XantaroDE/iC880A-Raspberry-PI/ch2i-orig/pictures/ch2i-gateway-monitoring-iot.jpg

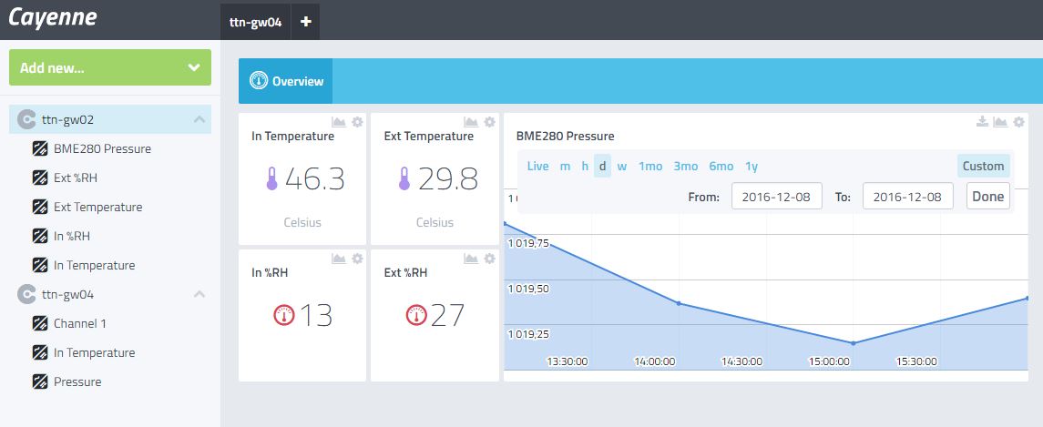
ch2i-orig/pictures/ch2i-gateway-monitoring-iot.jpg
