XantaroDE/iC880A-Raspberry-PI/ch2i-orig/pictures/ch2i-shield-lorawan-gateway.jpg

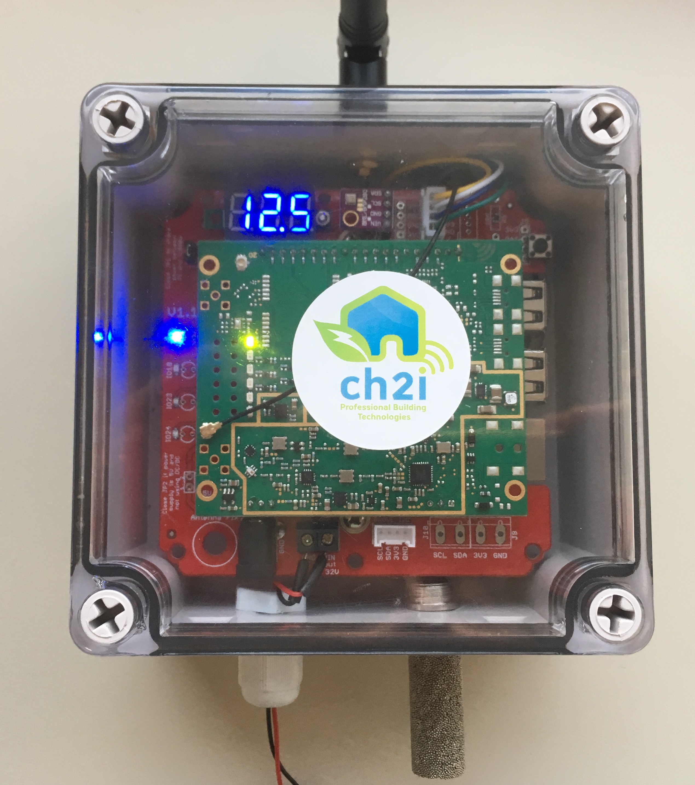
ch2i-orig/pictures/ch2i-shield-lorawan-gateway.jpg
