XantaroDE/iC880A-Raspberry-PI/ch2i-orig/pictures/iC880A-mounted-enclosure.jpg

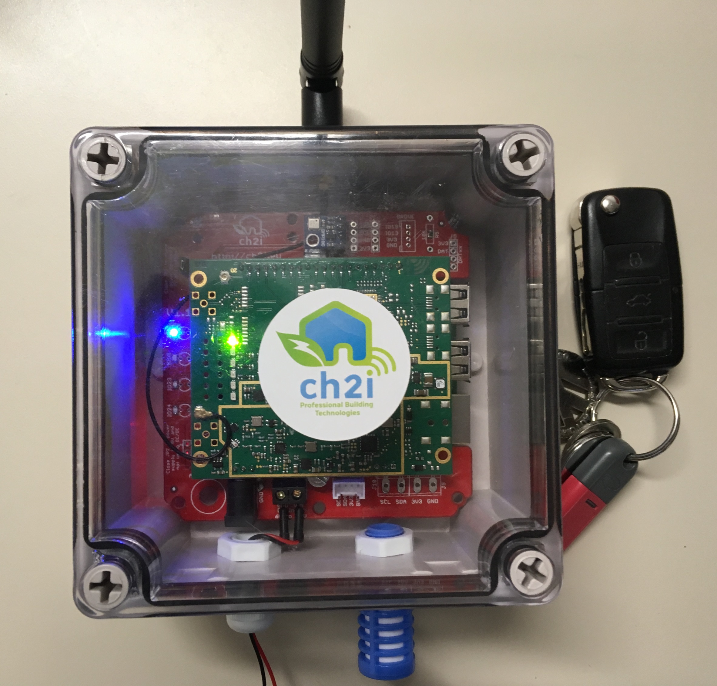
ch2i-orig/pictures/iC880A-mounted-enclosure.jpg
