XantaroDE/iC880A-Raspberry-PI/ch2i-orig/pictures/ic880a-mounted-V12.jpg

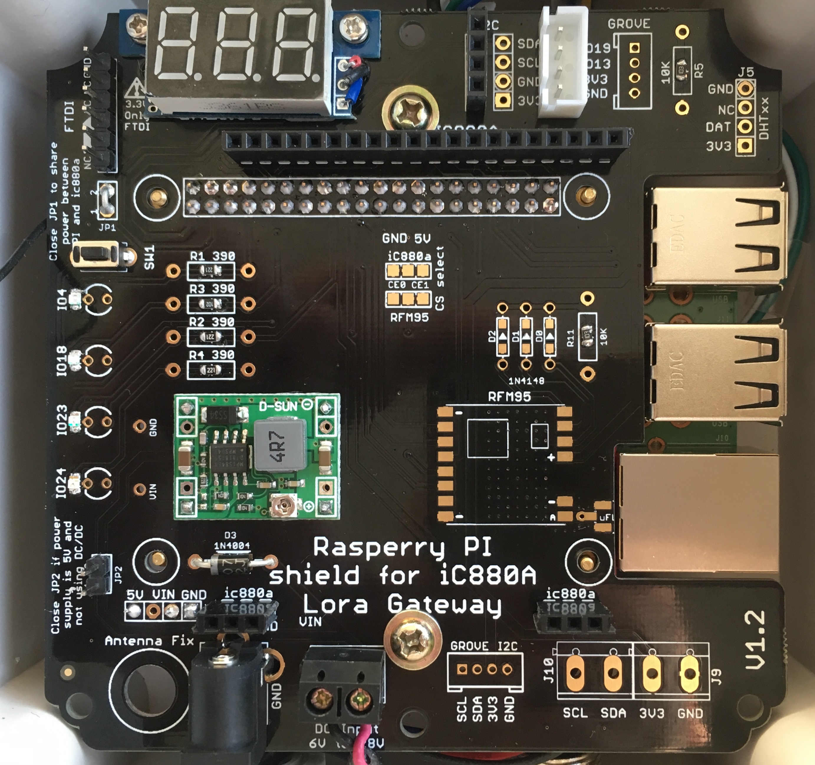
ch2i-orig/pictures/ic880a-mounted-V12.jpg
