XantaroDE/iC880A-Raspberry-PI/ch2i-orig/pictures/RPI-Lora-Gateway-mounted.jpg

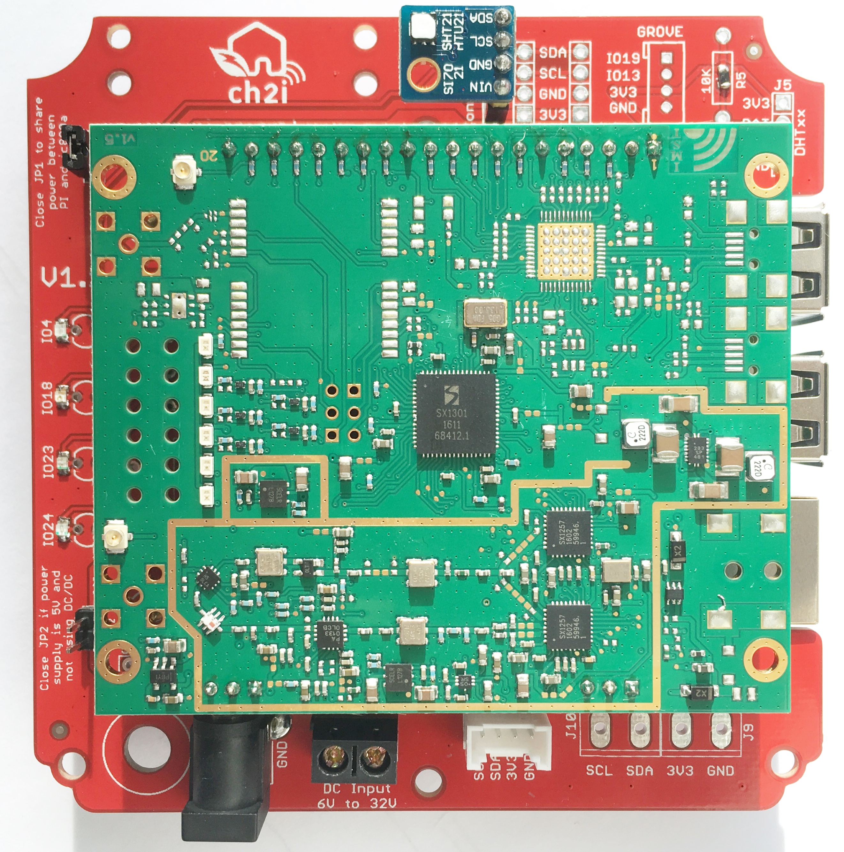
ch2i-orig/pictures/RPI-Lora-Gateway-mounted.jpg
