XantaroDE/iC880A-Raspberry-PI/ch2i-orig/pictures/RPI-Lora-Gateway-PCB.jpg

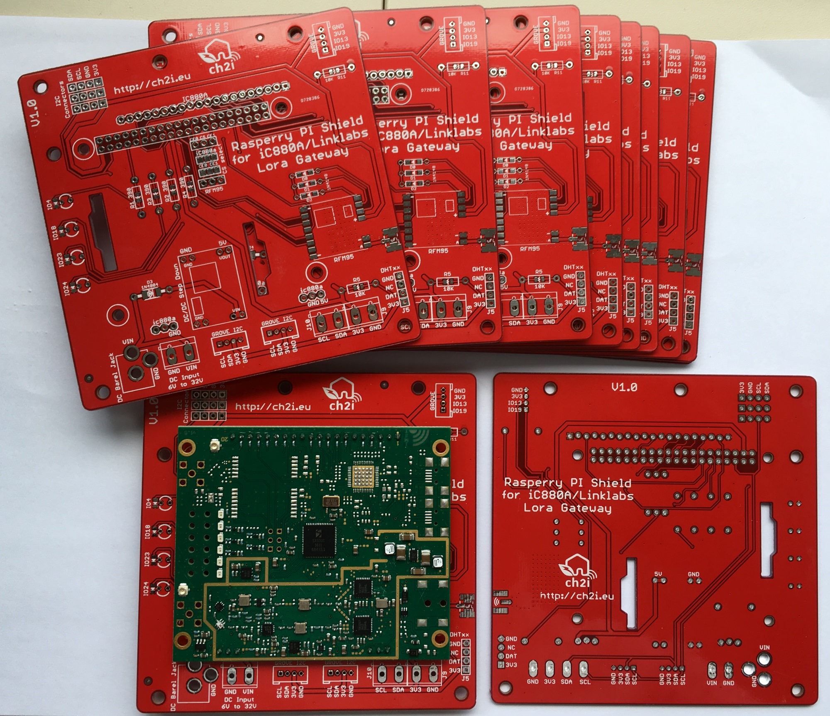
ch2i-orig/pictures/RPI-Lora-Gateway-PCB.jpg
