XantaroDE/iC880A-Raspberry-PI/ch2i-orig/pictures/RPI-Lora-Gateway-Shield-bot.png

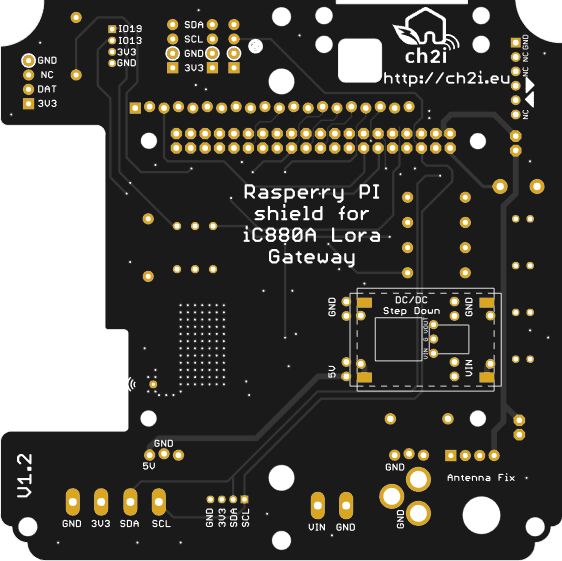
ch2i-orig/pictures/RPI-Lora-Gateway-Shield-bot.png
