XantaroDE/iC880A-Raspberry-PI/ch2i-orig/pictures/RPI-Lora-Gateway-Shield-sch.png

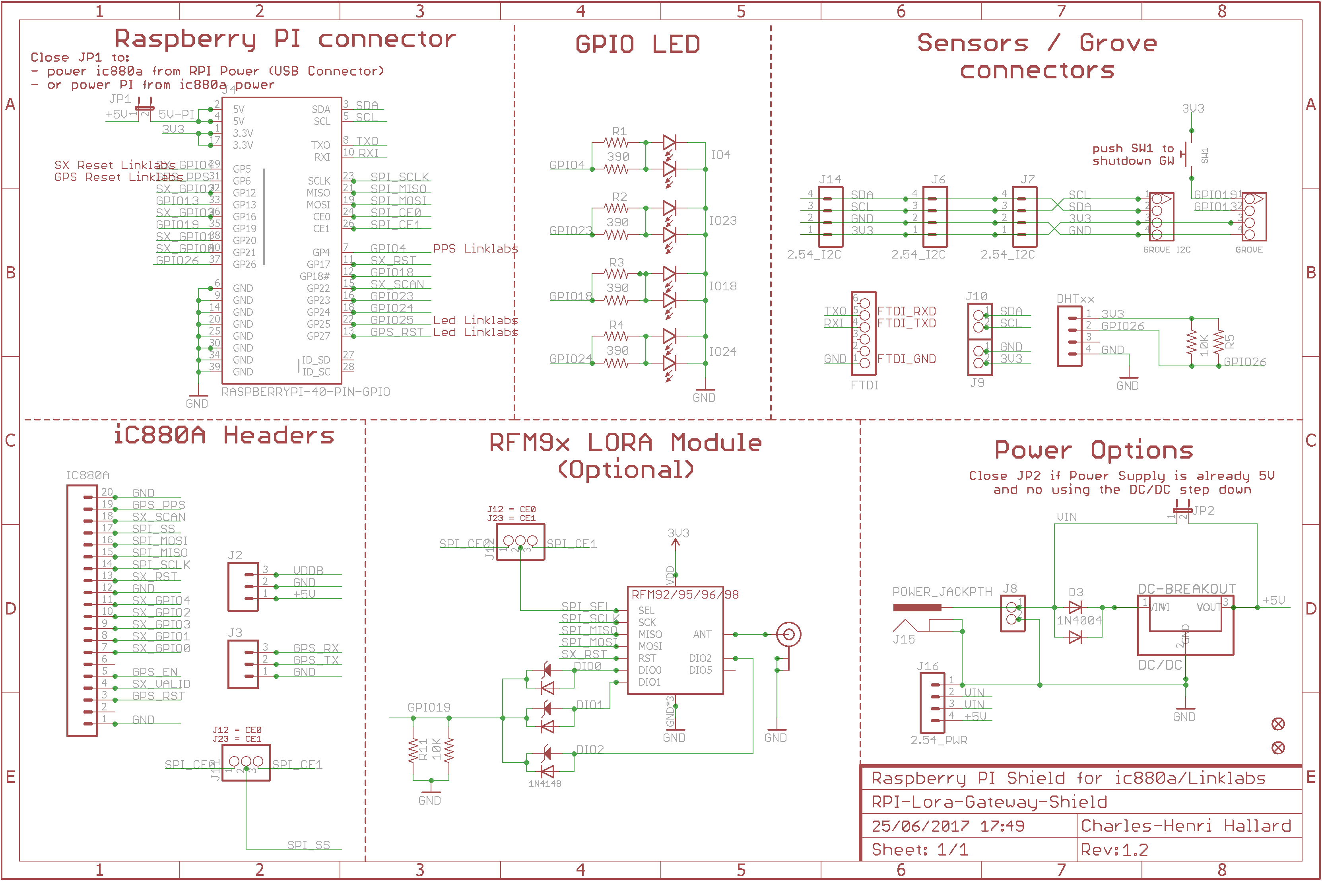
ch2i-orig/pictures/RPI-Lora-Gateway-Shield-sch.png
