XantaroDE/iC880A-Raspberry-PI/ch2i-orig/pictures/RPI-Lora-Gateway-Shield-top.jpg

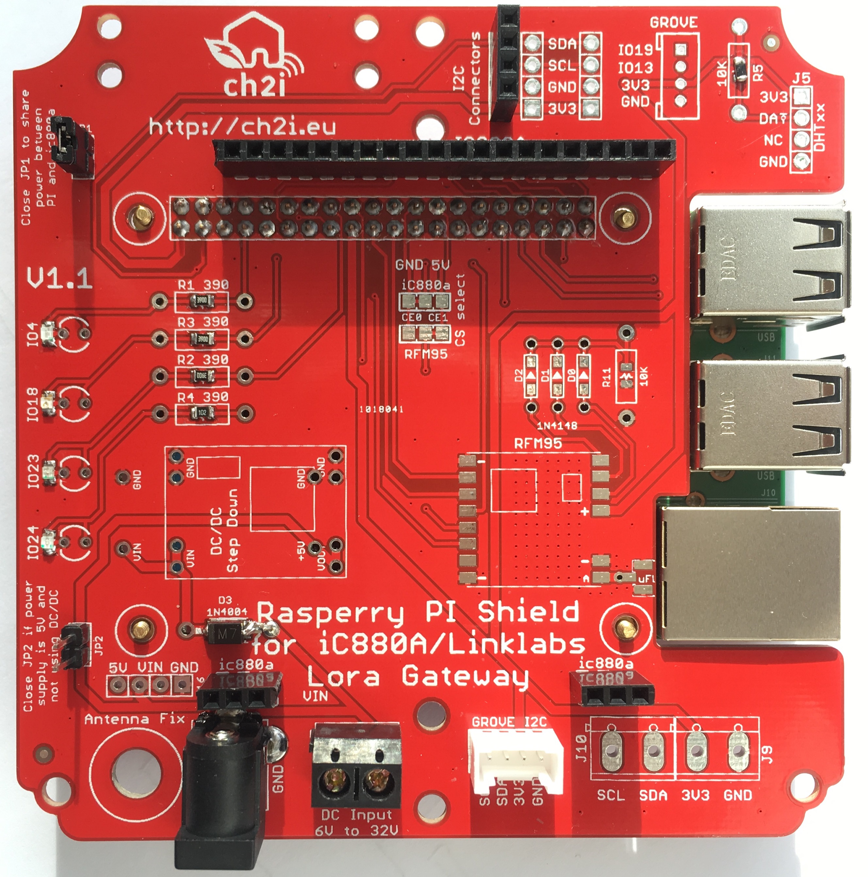
ch2i-orig/pictures/RPI-Lora-Gateway-Shield-top.jpg
